NathanTruong0930/E-muffler/Project Schedule/Gantt Chart.pdf

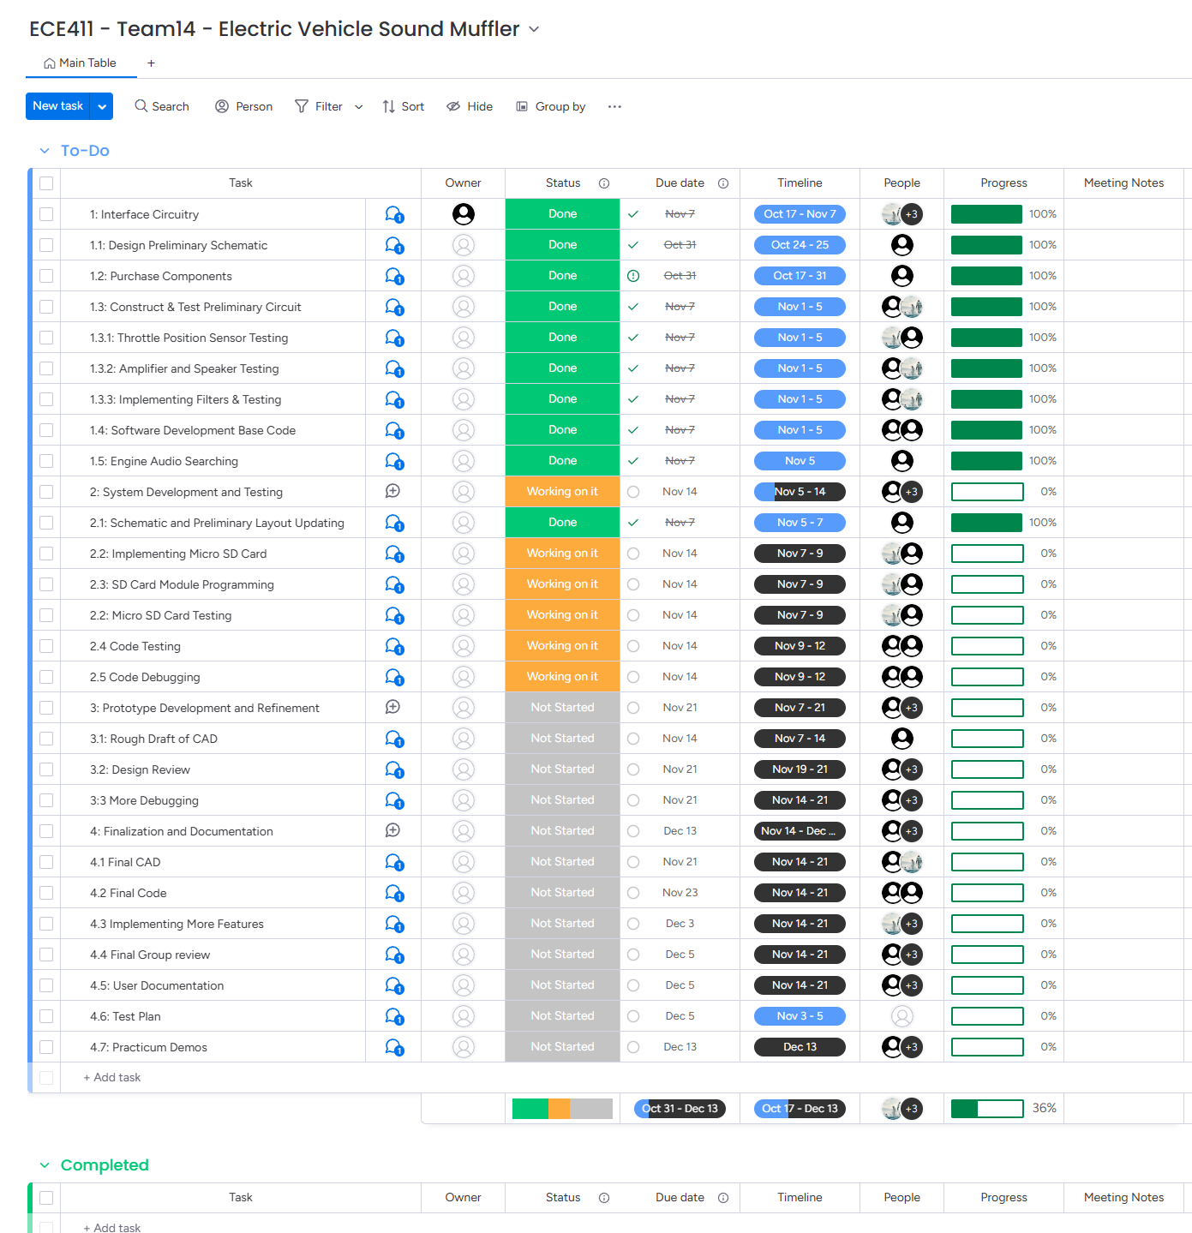
[picture p7: page 1]
