NathanTruong0930/E-muffler/Schematics/Final CAD - PCB - Version5.pdf

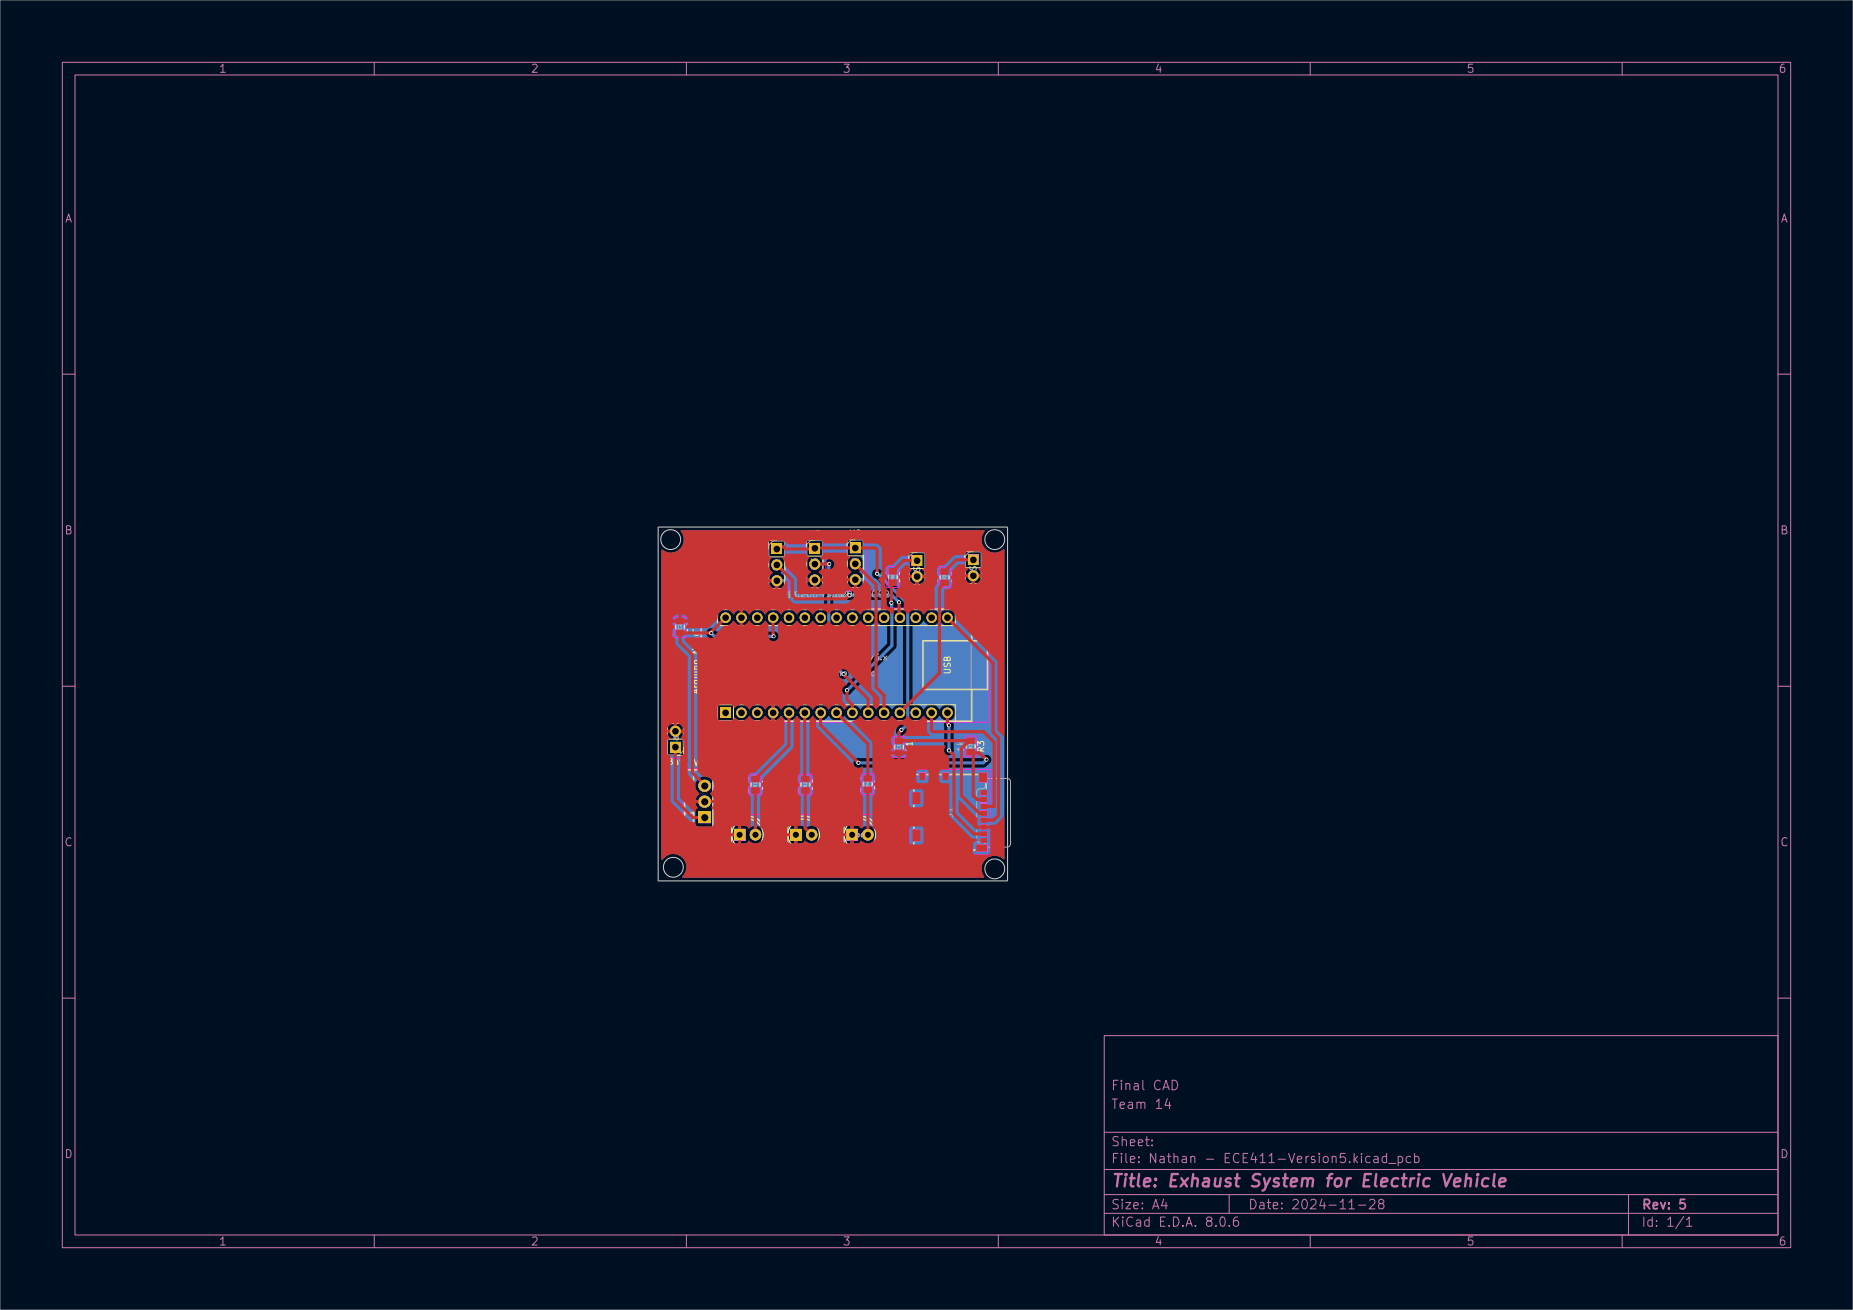
[picture p20: page 1]
