NathanTruong0930/E-muffler/Schematics/Final CAD - Schematic - Version5.pdf

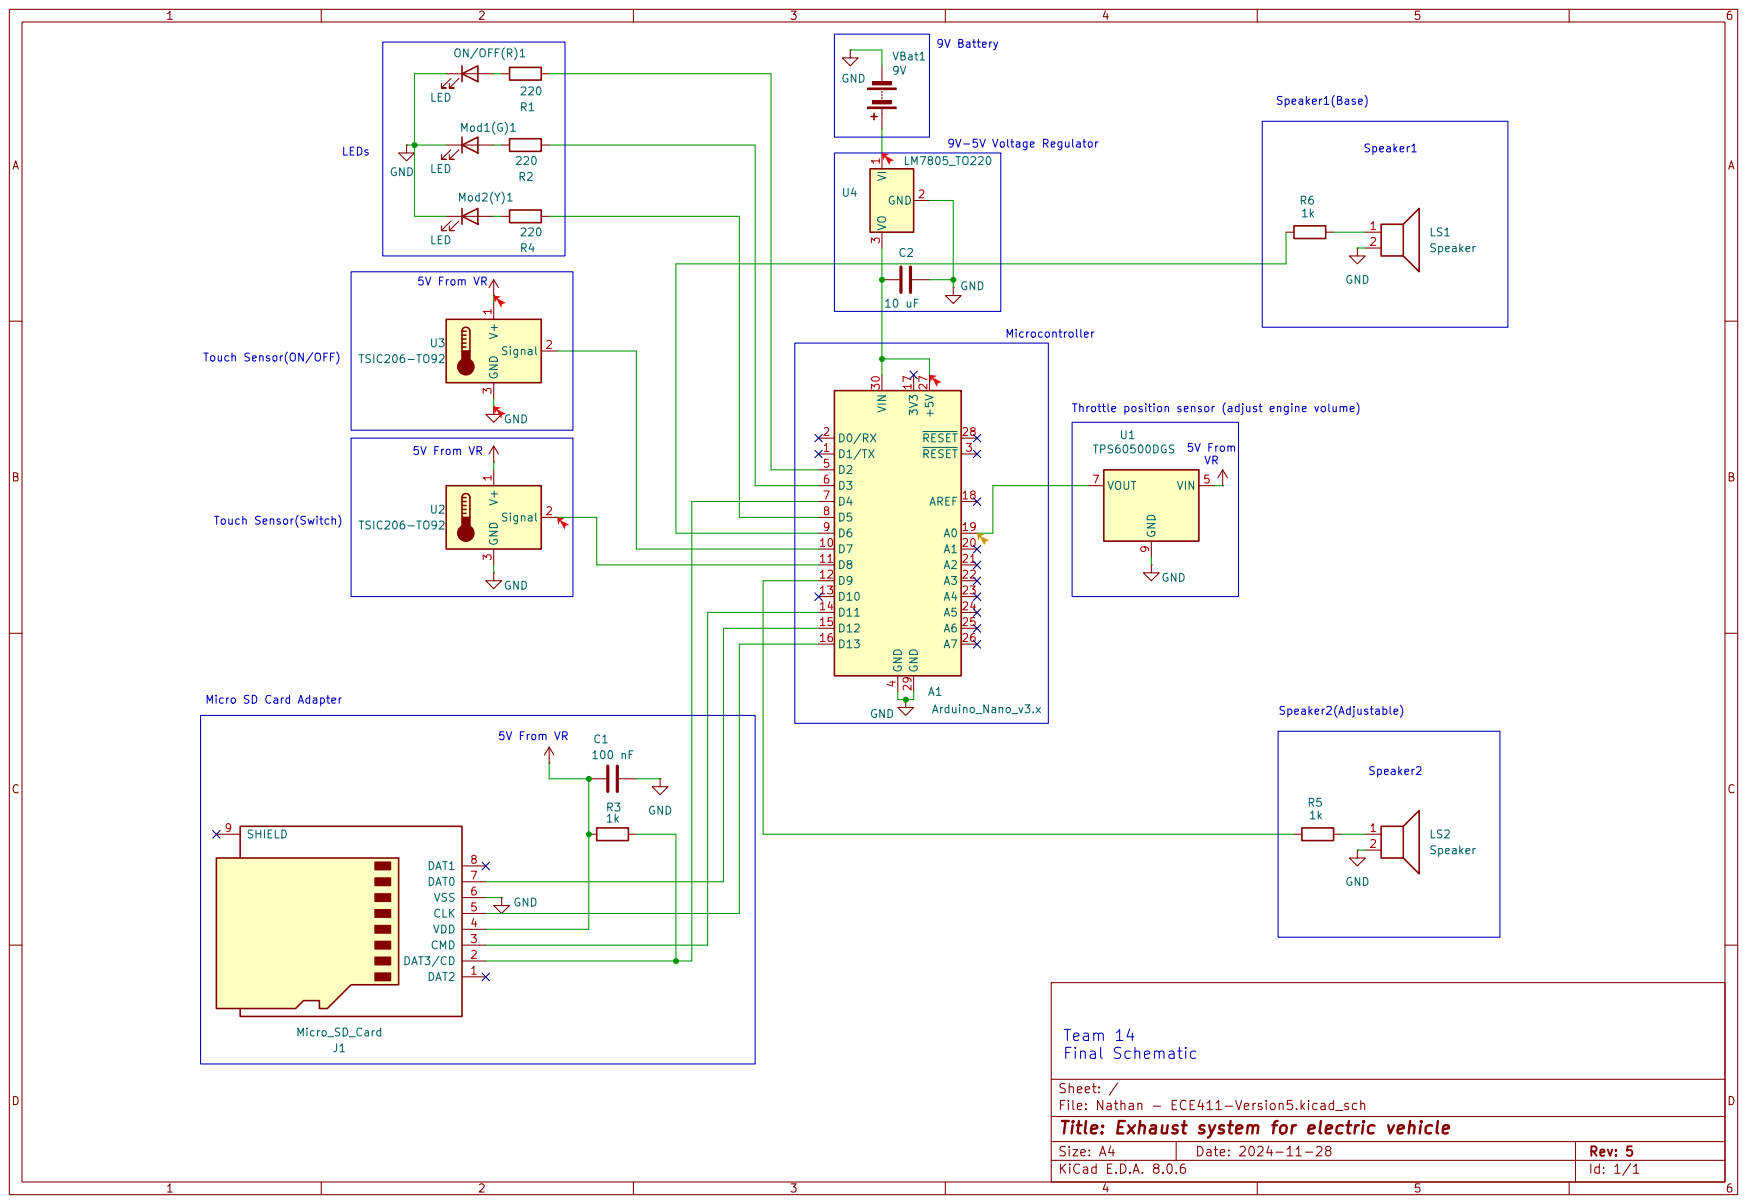
[picture p21: page 1]
