NathanTruong0930/E-muffler/Schematics/Final CAD - PCB - Version4.pdf

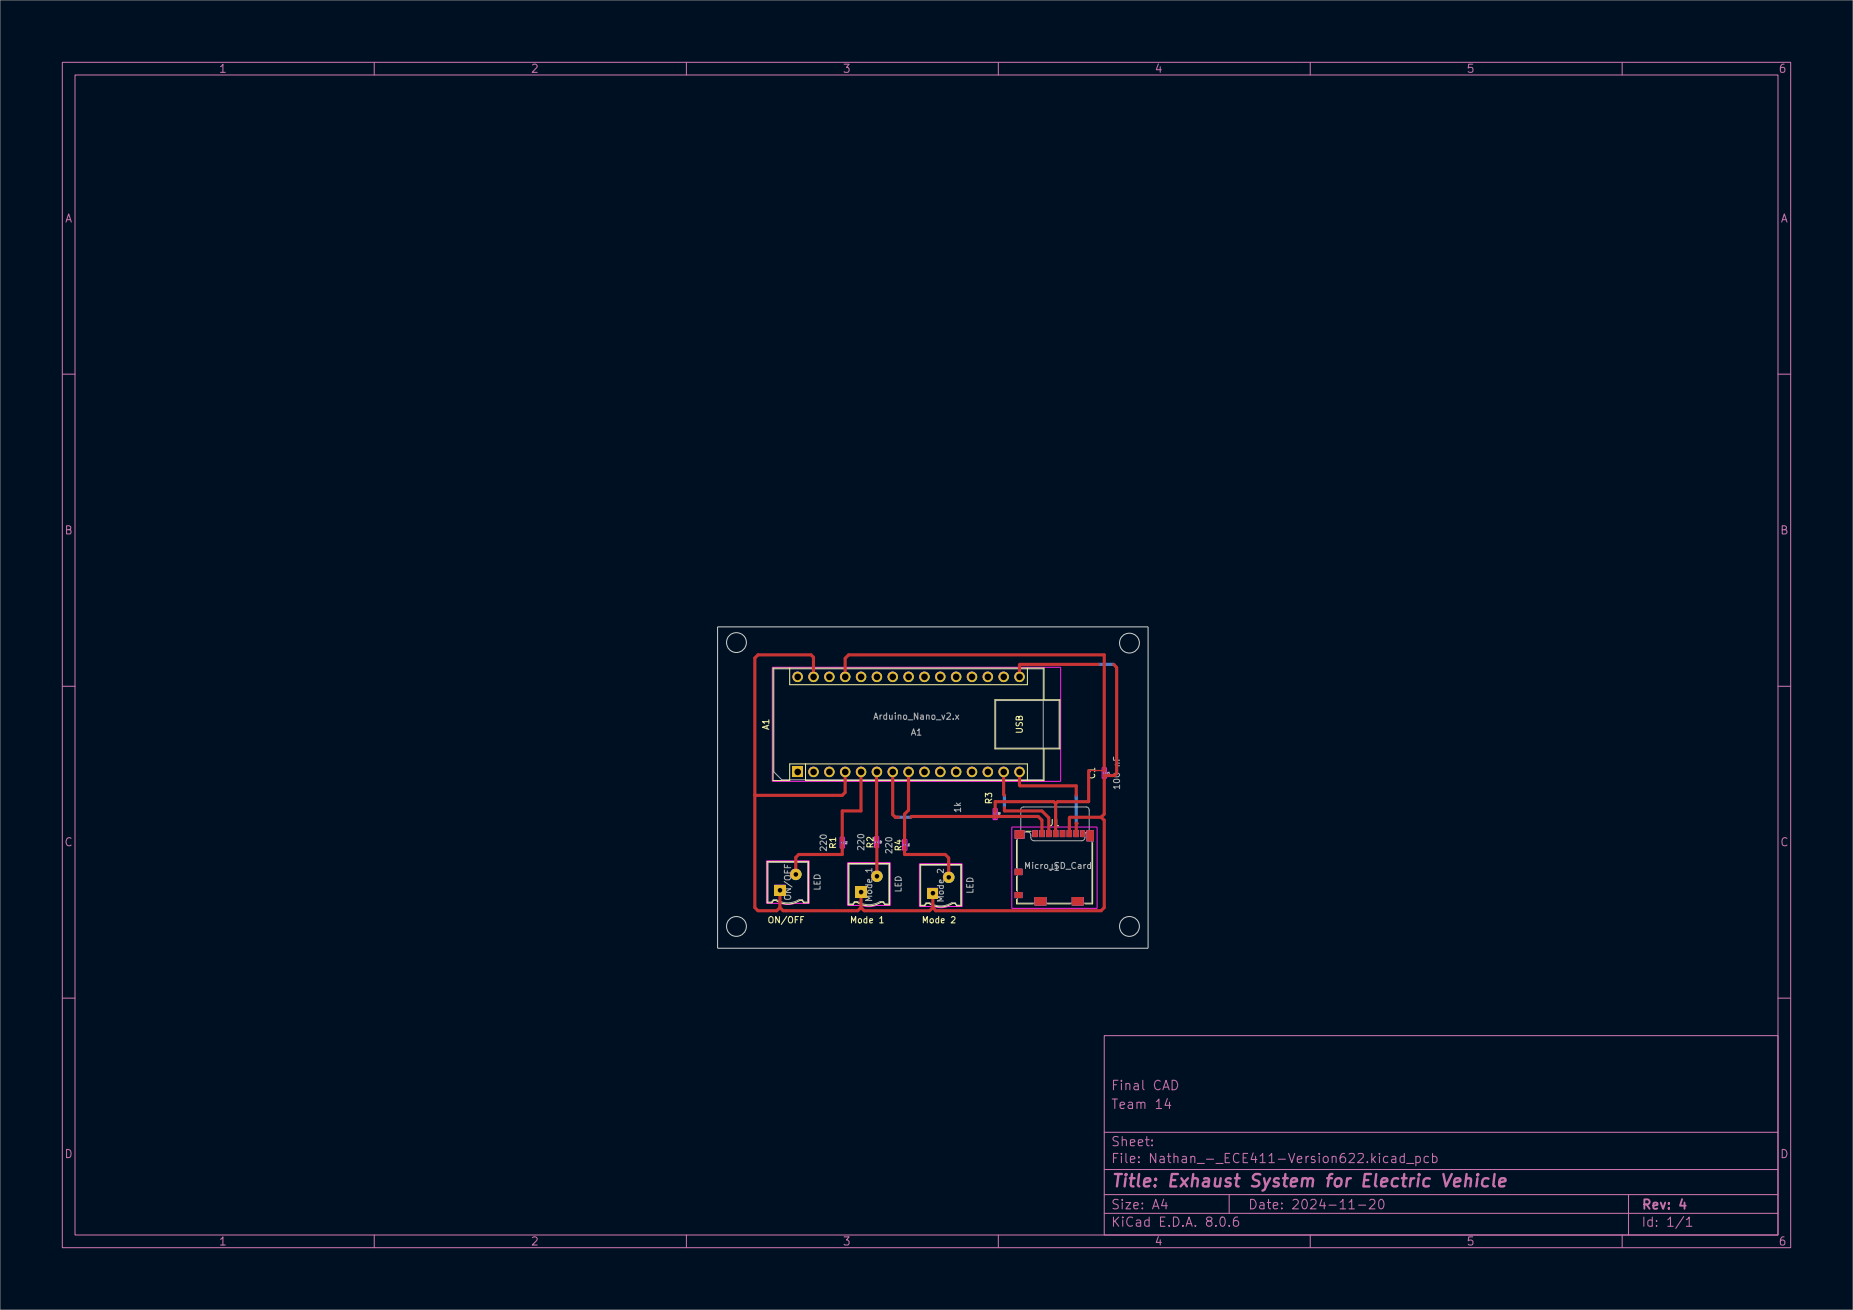
[picture p22: page 1]
