NathanTruong0930/E-muffler/Schematics/Final CAD - Schematic - Version4.pdf

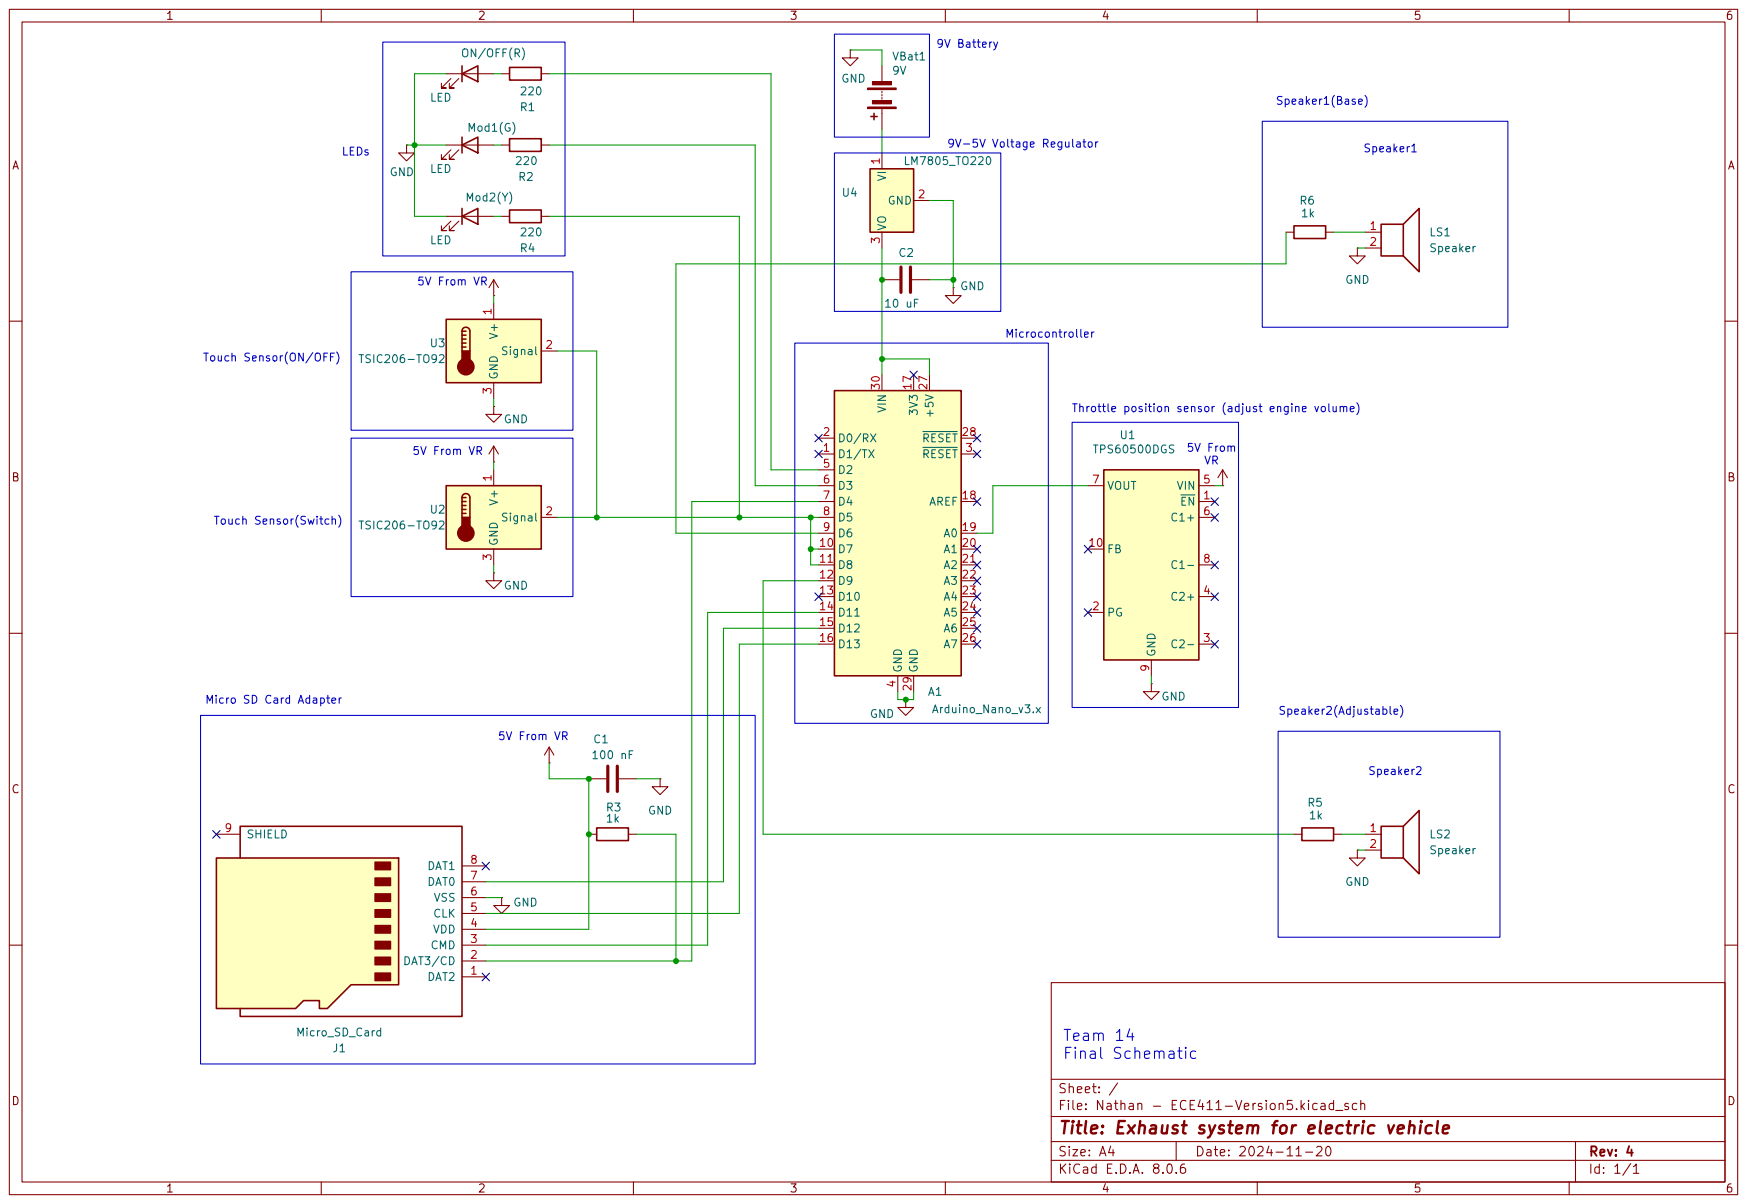
[picture p23: page 1]
